RobertPHeller/2ndGenLocoControlStand/ESP32-S3-WROOM-ControlStand/firmware/components/NvsManager/NvsManager.cpp

// -!- C++ -!- //////////////////////////////////////////////////////////////
//
//  System        : 
//  Module        : 
//  Object Name   : $RCSfile$
//  Revision      : $Revision$
//  Date          : $Date$
//  Author        : $Author$
//  Created By    : Robert Heller
//  Created       : Fri Dec 16 12:34:46 2022
//  Last Modified : <221218.1332>
//
//  Description	
//
//  Notes
//
//  History
//	
/////////////////////////////////////////////////////////////////////////////
//
//    Copyright (C) 2022  Robert Heller D/B/A Deepwoods Software
//			51 Locke Hill Road
//			Wendell, MA 01379-9728
//
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
// 
//
//////////////////////////////////////////////////////////////////////////////

static const char rcsid[] = "@(#) : $Id$";

#include "NvsManager.hxx"
#include "NodeIdMemoryConfigSpace.hxx"
#include "WiFiMemoryConfigSpace.hxx"
#include "sdkconfig.h"
#include <esp_err.h>
#include <esp_partition.h>
#include <esp_wifi_types.h>
#include <freertos_drivers/esp32/Esp32WiFiManager.hxx>
#include <nvs.h>
#include <nvs_flash.h>
#include <openlcb/SimpleStack.hxx>
using std::string;
#include <utils/format_utils.hxx>
#include <utils/logging.h>

#ifndef CONFIG_WIFI_STATION_SSID
#define CONFIG_WIFI_STATION_SSID ""
#endif

#ifndef CONFIG_WIFI_STATION_PASSWORD
#define CONFIG_WIFI_STATION_PASSWORD ""
#endif

#ifndef CONFIG_WIFI_HOSTNAME_PREFIX
#define CONFIG_WIFI_HOSTNAME_PREFIX "esp32throttle_"
#endif

namespace esp32s3controlstand {

static uninitialized<WiFiMemoryConfigSpace> wifi_memory_space;
static uninitialized<NodeIdMemoryConfigSpace> node_id_memoryspace;

/// NVS Persistence namespace.
const char NvsManager::NVS_NAMESPACE[];

/// NVS Persistence key.
const char NvsManager::NVS_CFG_KEY[];

DEFINE_SINGLETON_INSTANCE(NvsManager);

void NvsManager::init(uint8_t reset_reason)
{
    LOG(VERBOSE, "NVS.init(%d)", reset_reason);
    
    nvs_handle_t nvs;
    size_t config_size = sizeof(config_);
    
    // Initialize NVS before we do any other initialization as it may be
    // internally used by various components even if we disable it's usage in
    // the WiFi connection stack.
    LOG(INFO, "[NVS] Initializing NVS");
    if (ESP_ERROR_CHECK_WITHOUT_ABORT(nvs_flash_init()) == ESP_ERR_NVS_NO_FREE_PAGES)
    {
        const esp_partition_t *partition =
              esp_partition_find_first(ESP_PARTITION_TYPE_DATA,
                                       ESP_PARTITION_SUBTYPE_DATA_NVS, NULL);
        if (partition != NULL)
        {
            LOG(INFO, "[NVS] Erasing partition %s...", partition->label);
            ESP_ERROR_CHECK(esp_partition_erase_range(partition, 0, partition->size));
            ESP_ERROR_CHECK(nvs_flash_init());
        }
    }
    LOG(INFO, "[NVS] Loading configuration");
    // load non-CDI based config from NVS
    ESP_ERROR_CHECK(nvs_open(NVS_NAMESPACE, NVS_READWRITE, &nvs));
    esp_err_t res = ESP_ERROR_CHECK_WITHOUT_ABORT(
                 nvs_get_blob(nvs, NVS_CFG_KEY, &config_, &config_size));
    need_persist_ = false;
    if (config_size != sizeof(config_) || res != ESP_OK)
    {
        LOG_ERROR("[NVS] Configuration missing or corrupt, using defaults");
        memset(&config_, 0, sizeof(config_));
        config_.node_id = CONFIG_OLCB_NODE_ID;
        config_.force_reset = false;
        config_.reset_events_req = false;
        config_.bootloader_req = false;
        config_.wifi_mode = (wifi_mode_t)CONFIG_WIFI_MODE;
        strncpy(config_.hostname_prefix,CONFIG_WIFI_HOSTNAME_PREFIX,
                sizeof(config_.hostname_prefix));
        strncpy(config_.station_ssid,CONFIG_WIFI_STATION_SSID,
                sizeof(config_.station_ssid));
        strncpy(config_.station_pass,CONFIG_WIFI_STATION_PASSWORD,
                sizeof(config_.station_pass));
        need_persist_ = true;
    }
    CheckPersist();
    DisplayNvsConfiguration();
}

void NvsManager::DisplayNvsConfiguration()
{
    static constexpr const char *const WIFI_MODES[] =
    {
        "Disabled",
        "Station"
    };
    // display current configuration settings.
    LOG(INFO, "[NVS] Node ID: %s", utils::node_id_to_string(config_.node_id).c_str());
    LOG(INFO, "[NVS] Force Reset: %s",
        config_.force_reset ? "true" : "false");
    LOG(INFO, "[NVS] Reset events: %s",
        config_.reset_events_req ? "true" : "false");
    LOG(INFO, "[NVS] Bootloader: %s",
        config_.bootloader_req ? "true" : "false");
    LOG(INFO, "[NVS] WiFi Mode: %s (%d)", WIFI_MODES[config_.wifi_mode],
        config_.wifi_mode);
    LOG(INFO, "[NVS] Hostname Prefix: %s", config_.hostname_prefix);
    if (config_.wifi_mode != 0)
    {
        LOG(INFO, "[NVS] Station SSID: %s", config_.station_ssid);
    }
}

void NvsManager::register_virtual_memory_spaces(openlcb::SimpleStackBase *stack)
{
    node_id_memoryspace.emplace(stack, this);
    wifi_memory_space.emplace(stack, this);
}

}
