RobertPHeller/2ndGenLocoControlStand/ESP32ControlStand/ESP32ControlStand_Node/config.h

// -!- c++ -!- //////////////////////////////////////////////////////////////
//
//  System        : 
//  Module        : 
//  Object Name   : $RCSfile$
//  Revision      : $Revision$
//  Date          : $Date$
//  Author        : $Author$
//  Created By    : Robert Heller
//  Created       : Mon Oct 7 10:48:07 2019
//  Last Modified : <191011.2154>
//
//  Description	
//
//  Notes
//
//  History
//	
/////////////////////////////////////////////////////////////////////////////
//
//    Copyright (C) 2019  Robert Heller D/B/A Deepwoods Software
//			51 Locke Hill Road
//			Wendell, MA 01379-9728
//
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
// 
//
//////////////////////////////////////////////////////////////////////////////

#ifndef __CONFIG_H
#define __CONFIG_H
#include "openlcb/ConfiguredConsumer.hxx"
#include "openlcb/ConfiguredProducer.hxx"
#include "openlcb/ConfigRepresentation.hxx"
#include "openlcb/MemoryConfig.hxx"

#include "freertos_drivers/esp32/Esp32WiFiConfiguration.hxx"
#include "ESP32ControlStand.h"

// catch invalid configuration at compile time
#if !defined(USE_CAN) && !defined(USE_WIFI)
#error "Invalid configuration detected, USE_CAN or USE_WIFI must be defined."
#endif

namespace openlcb
{

/// Defines the identification information for the node. The arguments are:
///
/// - 4 (version info, always 4 by the standard
/// - Manufacturer name
/// - Model name
/// - Hardware version
/// - Software version
///
/// This data will be used for all purposes of the identification:
///
/// - the generated cdi.xml will include this data
/// - the Simple Node Ident Info Protocol will return this data
/// - the ACDI memory space will contain this data.
extern const SimpleNodeStaticValues SNIP_STATIC_DATA = {
    4,
    "OpenMRN",
#if defined(USE_WIFI) && !defined(USE_CAN)
    "ESP32 (Arduino) Throttle (WiFi)",
#elif defined(USE_CAN) && !defined(USE_WIFI)
    "ESP32 (Arduino) Throttle (CAN)",
#elif defined(USE_CAN) && defined(USE_WIFI)
    "ESP32 (Arduino) Throttle (WiFi/CAN)",
#else
    "ESP32 (Arduino) Throttle",
#endif
    ARDUINO_VARIANT,
    "1.00"};

#if defined(MCP23017_0) || defined(MCP23017_1)
constexpr uint8_t NUM_OUTPUTS = 8;
constexpr uint8_t NUM_INPUTS = 8;

/// Declares a repeated group of a given base group and number of repeats. The
/// ProducerConfig and ConsumerConfig groups represent the configuration layout
/// needed by the ConfiguredProducer and ConfiguredConsumer classes, and come
/// from their respective hxx file.
using AllConsumers = RepeatedGroup<ConsumerConfig, NUM_OUTPUTS>;
using AllProducers = RepeatedGroup<ProducerConfig, NUM_INPUTS>;

CDI_GROUP(mcpConfiguration);
CDI_GROUP_ENTRY(consumers, AllConsumers, Name("Outputs"));
CDI_GROUP_ENTRY(producers, AllProducers, Name("Inputs"));
CDI_GROUP_END();

#endif

/// Modify this value every time the EEPROM needs to be cleared on the node
/// after an update.
static constexpr uint16_t CANONICAL_VERSION = 0x1000;


/// Defines the main segment in the configuration CDI. This is laid out at
/// origin 128 to give space for the ACDI user data at the beginning.
CDI_GROUP(IoBoardSegment, Segment(MemoryConfigDefs::SPACE_CONFIG), Offset(128));
/// Each entry declares the name of the current entry, then the type and then
/// optional arguments list.
CDI_GROUP_ENTRY(internal_config, InternalConfigData);
#if defined(MCP23017_0)
CDI_GROUP_ENTRY(mcp0,mcpConfiguration,Name("MCP23017 #1 Configuration"));
#endif
#if defined(MCP23017_1)
CDI_GROUP_ENTRY(mcp1,mcpConfiguration,Name("MCP23017 #2 Configuration"));
#endif
#if defined(USE_WIFI)
CDI_GROUP_ENTRY(wifi, WiFiConfiguration, Name("WiFi Configuration"));
#endif
CDI_GROUP_ENTRY(controlstand,ESP32ControlStandConfig,Name("ESP32 Control Stand Configuration"));
CDI_GROUP_END();

/// This segment is only needed temporarily until there is program code to set
/// the ACDI user data version byte.
CDI_GROUP(VersionSeg, Segment(MemoryConfigDefs::SPACE_CONFIG),
    Name("Version information"));
CDI_GROUP_ENTRY(acdi_user_version, Uint8ConfigEntry,
    Name("ACDI User Data version"), Description("Set to 2 and do not change."));
CDI_GROUP_END();

/// The main structure of the CDI. ConfigDef is the symbol we use in main.cxx
/// to refer to the configuration defined here.
CDI_GROUP(ConfigDef, MainCdi());
/// Adds the <identification> tag with the values from SNIP_STATIC_DATA above.
CDI_GROUP_ENTRY(ident, Identification);
/// Adds an <acdi> tag.
CDI_GROUP_ENTRY(acdi, Acdi);
/// Adds a segment for changing the values in the ACDI user-defined
/// space. UserInfoSegment is defined in the system header.
CDI_GROUP_ENTRY(userinfo, UserInfoSegment);
/// Adds the main configuration segment.
CDI_GROUP_ENTRY(seg, IoBoardSegment);
/// Adds the versioning segment.
CDI_GROUP_ENTRY(version, VersionSeg);
CDI_GROUP_END();

} // namespace openlcb




#endif // __CONFIG_H
