RobertPHeller/2ndGenLocoControlStand/ESP32-S3-WROOM-ControlStand/firmware/components/NvsManager/BootPauseHelper.cpp

// -!- C++ -!- //////////////////////////////////////////////////////////////
//
//  System        : 
//  Module        : 
//  Object Name   : $RCSfile$
//  Revision      : $Revision$
//  Date          : $Date$
//  Author        : $Author$
//  Created By    : Robert Heller
//  Created       : Sat Dec 17 14:34:03 2022
//  Last Modified : <221218.1335>
//
//  Description	
//
//  Notes
//
//  History
//	
/////////////////////////////////////////////////////////////////////////////
//
//    Copyright (C) 2022  Robert Heller D/B/A Deepwoods Software
//			51 Locke Hill Road
//			Wendell, MA 01379-9728
//
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
// 
//
//////////////////////////////////////////////////////////////////////////////

static const char rcsid[] = "@(#) : $Id$";

#include <esp_err.h>
#include <esp_log.h>
#include <esp_ota_ops.h>
#include <esp_system.h>
#include <esp_task_wdt.h>
#include <esp32s3/rom/rtc.h>
#include <driver/uart.h>
#include "NvsManager.hxx"
#include "BootPauseHelper.hxx"
#include "utils/logging.h"
#include "string.h"
#include "NvsManager.hxx"

namespace esp32s3controlstand
{
void BootPauseHelper::CheckPause()
{
        bool need_driver_unload = !uart_is_driver_installed(UART_NUM_0);
    LOG(VERBOSE,"[CheckPause] need_driver_unload = %d",need_driver_unload);
    if (need_driver_unload)
    {
        esp_err_t res = uart_driver_install(UART_NUM_0,RXBufferLength,
                                            0,0,NULL,0);
        if (res != ESP_OK)
        {
            LOG_ERROR("[CheckPause] Failed to start UART");
            return;
        }
    }
    size_t bytesavailable;
    for (int i=0;i<PauseLoopCount;i++)
    {
        esp_err_t res = uart_get_buffered_data_len(UART_NUM_0,&bytesavailable);
        if (res != ESP_OK)
        {
            LOG_ERROR("[CheckPause] Failed to get buffered data len");
            return;
        }
        if (bytesavailable > 0)
        {
            break;
        }
        esp_rom_delay_us(PauseLoopDelay_us);
    }
    if (bytesavailable > 0)
    {
        PauseConsole();
        NvsManager::instance()->CheckPersist();
    }
    if (need_driver_unload)
    {
        esp_err_t res = uart_driver_delete(UART_NUM_0);
        if (res != ESP_OK)
        {
            LOG_ERROR("[CheckPause] Failed to delete uart");
            return;
        }
    }
}

void BootPauseHelper::PauseConsole()
{
    char receivebuffer[RXBufferLength];
    char transmitBuffer[TXBufferLength];
    
    uart_write_bytes(UART_NUM_0,"Ready.\r\n",8);
    
    while (true)
    {
        uart_write_bytes(UART_NUM_0,"\r\n>>>",5);
        size_t len = ReadLine(UART_NUM_0,receivebuffer,sizeof(receivebuffer));
        if (len == 0)
        {
            continue;
        }
        switch (toupper(receivebuffer[0]))
        {
        case SETNODE:
            {
                uint64_t nid = ParseNode(&receivebuffer[1],len-1);
                uart_write_bytes(UART_NUM_0,"\r\n",2);
                NvsManager::instance()->node_id(nid);
                int l = snprintf(transmitBuffer,sizeof(transmitBuffer),"\r\nSet Node ID: %0llx\r\n",nid);
                uart_write_bytes(UART_NUM_0,transmitBuffer,l);
                break;
            }
        case BOOTLOADER:
            NvsManager::instance()->force_bootloader();
            break;
        case EVENTRESET:
            NvsManager::instance()->force_reset_events();
            break;
        case FACTORYRESET:
            NvsManager::instance()->force_factory_reset();
            break;
        case SETSSID:
            NvsManager::instance()->station_ssid(GetString(&receivebuffer[1],len-1));
            break;
        case SETPASS:
            NvsManager::instance()->station_pass(GetString(&receivebuffer[1],len-1));
            break;
        case SETHOST:
            NvsManager::instance()->hostname_prefix(GetString(&receivebuffer[1],len-1));
            break;
        case SETWIFI:
            NvsManager::instance()->wifi_mode(GetMode(&receivebuffer[1],len-1));
            break;
        case RESUME:
            return;
        default:
            {
                int l = snprintf(transmitBuffer,sizeof(transmitBuffer),"Err: %c\r\n",receivebuffer[0]);
                uart_write_bytes(UART_NUM_0,transmitBuffer,l);
                break;
            }
        }
    }
}

uint64_t BootPauseHelper::ParseNode(char * buffer, size_t bufferlen)
{
    uint64_t result = 0;
    char *p = NULL;
    size_t l = 0;
    for (p = buffer,l = bufferlen; l > 0 && *p != '\0';p++,l--)
    {
        if (isxdigit(*p))
        {
            if (isdigit(*p))
            {
                result = (result << 4) + (*p - '0');
            }
            else if (islower(*p))
            {
                result = (result << 4) + ((*p - 'a')+10);
            }
            else
            {
                result = (result << 4) + ((*p - 'A')+10);
            }
        }
    }
    return result;
}

size_t BootPauseHelper::ReadLine(uart_port_t uart_num,char *buffer,
                                 size_t bufferlen)
{
    char *p = buffer;
    size_t remainder = bufferlen;
    size_t numread   = 0;
    const char space[] = "\b \b";
    const char eol[] = "\r\n";
    
    while (remainder > 0)
    {
        int r = uart_read_bytes(uart_num,p,1,100);
        if (r > 0)
        {
            if (*p == EOL)
            {
                uart_write_bytes(uart_num,eol,2);
                numread++;
                *p = '\0';
                break;
            }
            else if (*p == '\b' || *p == 0x7f)
            {
                if (p > buffer && remainder < bufferlen)
                {
                    p--; remainder++; numread--;
                    uart_write_bytes(uart_num,space,3);
                    
                }
            }
            else
            {
                uart_write_bytes(uart_num,p,r);
                numread++;
                p++;
                remainder--;
            }
        }
    }
    return numread;
}

wifi_mode_t BootPauseHelper::GetMode(char *buffer,size_t bufferlen)
{
    char *p = buffer;
    char *end = buffer+bufferlen;
    while (*p <= ' ' && p < end) p++;
    if (p >= end) return WIFI_MODE_STA;
    if (strncasecmp("ON",p,2) == 0) {return WIFI_MODE_STA;}
    else if (strncasecmp("OFF",p,3) == 0) {return WIFI_MODE_NULL;}
    else if (strncasecmp("YES",p,3) == 0) {return WIFI_MODE_STA;}
    else if (strncasecmp("NO",p,2) == 0) {return WIFI_MODE_NULL;}
    else {return WIFI_MODE_STA;}
}

const char *BootPauseHelper::GetString(char *buffer,size_t bufferlen)
{
    char *p = buffer;
    char *end = buffer+bufferlen;
    while (*p <= ' ' && p < end) p++;
    if (p >= end) return "";
    while (*(end-1) <= ' ' && end > p) end--;
    *end = '\0';
    return p;
}



DEFINE_SINGLETON_INSTANCE(BootPauseHelper);

}
